LaskaKit/microESP/SW/esp32-c3_ADC_OLED/esp32-c3_ADC_OLED.ino

/*
* This example code is used for LaskaKit microESP32-C3 board 
*
* MicroESP32-C3 board reads voltage on Battery  
* and sends every 2 seconds through UART or native USB (depends on setting, read below) and OLED display
* 
* !!! ESP library version !!!
* ESP32 library 3.0.x
* Condition: Tools -> if USB CDC On Boot is ENABLED then
* Serial means native USB
* Tools -> if USB CDC On Boot is DISABLED then
* Serial means UART
* ---
* ESP32 library 2.0.xy
* Condition: Tools -> USB CDC On Boot must be disabled
* use USBSerial to send data through native USB 
*
* Board: ESP32-C3 Dev Module
* 
*/
#include <SPI.h>
#include <Wire.h>
#include <Adafruit_GFX.h>
#include <Adafruit_SH110X.h>

#define SDA 8
#define SCL 10
#define ADCBpin 0
#define bDeviderRatio 1.7693877551  // Voltage devider ratio on ADC pin 1MOhm + 1.3MOhm
#define SCREEN_ADDRESS 0x3C // or 0x3D
Adafruit_SH1106G display = Adafruit_SH1106G(128, 64, &Wire, -1); //Nastavit display

void setup() {

  Serial.begin(115200);
  while(!Serial);    // time to get serial running

  Wire.begin(SDA,SCL);
  
  display.begin(SCREEN_ADDRESS, true); 
  display.clearDisplay(); 
  display.setTextColor(SH110X_WHITE); 
  display.setTextSize(1); 

}

void loop() {

  float bat_voltage = analogReadMilliVolts(ADCBpin) * bDeviderRatio / 1000;
  Serial.print("Battery Voltage = " );
  Serial.print(bat_voltage);
  Serial.println("V");

  display.clearDisplay();

  display.setTextSize(1.8);      // Normal 1:1 pixel scale
  display.setTextColor(SH110X_WHITE);
  display.setCursor(0, 0);     // Start at top-left corner
  display.cp437(true);         // Use full 256 char 'Code Page 437' font

  display.println("Battery: " + String(bat_voltage, 3));
  
  display.display();
  
  delay(2000);
}
